irsla/ZuruLegoMod/firmware/Core/Src/sdmmc.c

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
/* Includes ------------------------------------------------------------------*/
#include "sdmmc.h"

SD_HandleTypeDef hsd1;

/* SDMMC1 init function */

void MX_SDMMC1_SD_Init(void)
{

  /* USER CODE BEGIN SDMMC1_Init 0 */
  GPIO_PinState state = HAL_GPIO_ReadPin(SDMMC1_DETECT_GPIO_Port, SDMMC1_DETECT_Pin);
  if (hsd1.Instance == SDMMC1)  {
    return;
  }
  if (state == GPIO_PIN_SET) {
    // card is not inserted
    return;
  }
  /* USER CODE END SDMMC1_Init 0 */

  hsd1.Instance = SDMMC1;
  hsd1.Init.ClockEdge = SDMMC_CLOCK_EDGE_RISING;
  hsd1.Init.ClockPowerSave = SDMMC_CLOCK_POWER_SAVE_DISABLE;
  hsd1.Init.BusWide = SDMMC_BUS_WIDE_4B;
  hsd1.Init.HardwareFlowControl = SDMMC_HARDWARE_FLOW_CONTROL_DISABLE;
  hsd1.Init.ClockDiv = 0x01;
  if (HAL_SD_Init(&hsd1) != HAL_OK)
  {
    Error_Handler();
  }
  /* USER CODE BEGIN SDMMC1_Init 2 */
  //HAL_SD_ConfigSpeedBusOperation(&hsd1,SDMMC_SPEED_MODE_HIGH);
  /* USER CODE END SDMMC1_Init 2 */

}

void HAL_SD_MspInit(SD_HandleTypeDef* sdHandle)
{

  GPIO_InitTypeDef GPIO_InitStruct = {0};
  RCC_PeriphCLKInitTypeDef PeriphClkInitStruct = {0};
  if(sdHandle->Instance==SDMMC1)
  {
  /** Initializes the peripherals clock
  */
    PeriphClkInitStruct.PeriphClockSelection = RCC_PERIPHCLK_SDMMC1;
    PeriphClkInitStruct.Sdmmc1ClockSelection = RCC_SDMMC1CLKSOURCE_PLL1Q;
    if (HAL_RCCEx_PeriphCLKConfig(&PeriphClkInitStruct) != HAL_OK)
    {
      Error_Handler();
    }

    /* SDMMC1 clock enable */
    __HAL_RCC_SDMMC1_CLK_ENABLE();

    __HAL_RCC_GPIOC_CLK_ENABLE();
    __HAL_RCC_GPIOD_CLK_ENABLE();
    /**SDMMC1 GPIO Configuration
    PC8     ------> SDMMC1_D0
    PC9     ------> SDMMC1_D1
    PC10     ------> SDMMC1_D2
    PC11     ------> SDMMC1_D3
    PC12     ------> SDMMC1_CK
    PD2     ------> SDMMC1_CMD
    */
    GPIO_InitStruct.Pin = GPIO_PIN_8|GPIO_PIN_9|GPIO_PIN_10|GPIO_PIN_11
                          |GPIO_PIN_12;
    GPIO_InitStruct.Mode = GPIO_MODE_AF_PP;
    GPIO_InitStruct.Pull = GPIO_NOPULL;
    GPIO_InitStruct.Speed = GPIO_SPEED_FREQ_HIGH;
    GPIO_InitStruct.Alternate = GPIO_AF12_SDMMC1;
    HAL_GPIO_Init(GPIOC, &GPIO_InitStruct);

    GPIO_InitStruct.Pin = GPIO_PIN_2;
    GPIO_InitStruct.Mode = GPIO_MODE_AF_PP;
    GPIO_InitStruct.Pull = GPIO_NOPULL;
    GPIO_InitStruct.Speed = GPIO_SPEED_FREQ_HIGH;
    GPIO_InitStruct.Alternate = GPIO_AF12_SDMMC1;
    HAL_GPIO_Init(GPIOD, &GPIO_InitStruct);

    /* SDMMC1 interrupt Init */
    HAL_NVIC_SetPriority(SDMMC1_IRQn, 1, 0);
    HAL_NVIC_EnableIRQ(SDMMC1_IRQn);
  }
}

void HAL_SD_MspDeInit(SD_HandleTypeDef* sdHandle)
{

  if(sdHandle->Instance==SDMMC1)
  {
    /* Peripheral clock disable */
    __HAL_RCC_SDMMC1_CLK_DISABLE();

    /**SDMMC1 GPIO Configuration
    PC8     ------> SDMMC1_D0
    PC9     ------> SDMMC1_D1
    PC10     ------> SDMMC1_D2
    PC11     ------> SDMMC1_D3
    PC12     ------> SDMMC1_CK
    PD2     ------> SDMMC1_CMD
    */
    HAL_GPIO_DeInit(GPIOC, GPIO_PIN_8|GPIO_PIN_9|GPIO_PIN_10|GPIO_PIN_11
                          |GPIO_PIN_12);

    HAL_GPIO_DeInit(GPIOD, GPIO_PIN_2);

    /* SDMMC1 interrupt Deinit */
    HAL_NVIC_DisableIRQ(SDMMC1_IRQn);
  /* USER CODE BEGIN SDMMC1_MspDeInit 1 */
    sdHandle->Instance = NULL;
  /* USER CODE END SDMMC1_MspDeInit 1 */
  }
}

/* USER CODE BEGIN 1 */
void MX_SDMMC1_SD_Deinit(void) {
  HAL_SD_DeInit(&hsd1);
}
/* USER CODE END 1 */
